MarcFinns/AtmoScan/__ATMOSCAN_MASTER_V3.3.1/ScreenWeatherStationSettings.h

/*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
  Adapted by Bodmer to use the faster TFT_eSPI library:
  https://github.com/Bodmer/TFT_eSPI

*/

#pragma once


// Setup
const int UPDATE_INTERVAL_SECS = 10 * 60; // Update every 10 minutes

// TimeClient settings
const float UTC_OFFSET = 0;

// Wunderground Settings, EDIT TO SUIT YOUR LOCATION
const bool IS_METRIC = true; // Temperature only? Wind speed units appear to stay in mph. To do: investigate <<<<<<<<<<<<<<<<<<<<<<<<<
//const String WUNDERGRROUND_LANGUAGE PROGMEM = "EN";

// Windspeed conversion, use 1 pair of #defines. To do: investigate a more convenient method <<<<<<<<<<<<<<<<<<<<<
//#define WIND_SPEED_SCALING 1.0      // mph
//#define WIND_SPEED_UNITS " mph"

//#define WIND_SPEED_SCALING 0.868976 // mph to knots
//#define WIND_SPEED_UNITS " kn"

#define WIND_SPEED_SCALING 1.60934  // mph to kph
#define WIND_SPEED_UNITS " kph"

// List of 19 items, so that the downloader knows what to fetch
const char * const wundergroundIcons[] PROGMEM = {"chanceflurries", "chancerain", "chancesleet", "chancesnow", "clear", "cloudy", "flurries", "fog", "hazy", "mostlycloudy", "mostlysunny", "partlycloudy", "partlysunny", "rain", "sleet", "snow", "sunny", "tstorms", "unknown"};

const char URL1[] PROGMEM = "http://www.squix.org/blog/wunderground/";
const char URL2[] PROGMEM = "http://www.squix.org/blog/wunderground/mini/";
const char URL3[] PROGMEM = "http://www.squix.org/blog/moonphase_L";
const char FILETYPE[] PROGMEM = ".bmp";
const char MOON[] PROGMEM = "/moon";
const char MINI[] PROGMEM = "/mini/";



/***************************
   End Settings
 **************************/

// #endif
