MarcFinns/AtmoScan/__ATMOSCAN_MASTER_V3.3.1/ScreenWeatherStation.cpp

/*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
  Adapted by Bodmer to use the faster TFT_eSPI library:
  https://github.com/Bodmer/TFT_eSPI

  Plus:
  Minor changes to text placement and auto-blanking out old text with background colour padding
  Moon phase text added
  Forecast text lines are automatically split onto two lines at a central space (some are long!)
  Time is printed with colons aligned to tidy display
  Min and max forecast temperatures spaced out
  The ` character has been changed to a degree symbol in the 36 point font
  New smart WU splash startup screen and updated progress messages
  Display does not need to be blanked between updates
  Icons nudged about slightly to add wind direction
*/

#include <Syslog.h>               // https://github.com/arcao/ESP8266_Syslog
#include <TFT_eSPI.h>             // https://github.com/Bodmer/TFT_eSPI
#include "ScreenWeatherStation.h"
#include "ScreenWeatherStationSettings.h"
#include "WundergroundClient.h"
#include "GlobalDefinitions.h"

// Fonts created by http://oleddisplay.squix.ch/
#include "Free_Fonts.h"
#include "Fonts.h"

// Download helper
#include "WebResource.h"

// External variables
extern Syslog syslog;
extern TFT_eSPI LCD;
extern GfxUi ui;
extern struct Configuration config;
extern struct ProcessContainer procPtr;
extern WebResource webResource;

// Prototypes
void errLog(String msg);
void setTurbo(bool setTurbo);
bool isTurbo();



// Static variables
bool ScreenWeatherStation::wunderValid = false;
WundergroundClient *ScreenWeatherStation::wunderground;

void  ScreenWeatherStation::activate()
{
#ifdef DEBUG_SYSLOG
  syslog.log(LOG_INFO, F("ScreenWeatherStation::activate()"));
#endif

  LCD.fillScreen(TFT_BLACK);
  LCD.setFreeFont(&ArialRoundedMTBold_14);
  LCD.setTextColor(TFT_ORANGE, TFT_BLACK);

  if (!procPtr.GeoLocation.isValid() || !config.connected)
  {
    LCD.setTextDatum(TC_DATUM);
    LCD.drawString(F("Weather Station needs"), 120, 120, GFXFF);
    LCD.drawString(F("network & geolocation"), 120, 140, GFXFF);
    isInitialised = false;
    return;
  }

  // Create Wunderground object if not existent
  if (!wunderValid)
  {

#ifdef DEBUG_SYSLOG
    syslog.log(LOG_INFO, F("wunderground object did not exist, initialise it"));
#endif

    // TURBO mode
    setTurbo(true);

    wunderground = new WundergroundClient(IS_METRIC);
    wunderValid = true;

    // Print credits
    LCD.setTextDatum(BC_DATUM);
    LCD.setTextColor(TFT_WHITE, TFT_BLACK);
    LCD.drawString(F("By: blog.squix.org"), 120, 180);
    LCD.drawString(F("Adapted: Bodmer, MarcFinns"), 120, 195);

    LCD.setTextColor(TFT_ORANGE, TFT_BLACK);
    LCD.setFreeFont(&ArialRoundedMTBold_14);
    LCD.drawString(F("Downloading resources..."), 120, 220);

    // Splash screen - Download WU graphic jpeg first and display it, then the Earth view
    webResource.downloadFile(F("http://i.imgur.com/njl1pMj.jpg"), F("/wunder.jpg"));
    if (SPIFFS.exists(F("/wunder.jpg")) == true) ui.drawJpeg(F("/wunder.jpg"), 0, 10);

    //  webResource.downloadFile(F("http://i.imgur.com/v4eTLCC.jpg"), F("/Earth.jpg"));
    webResource.downloadFile(F("http://i.imgur.com/v4eTLCC.jpg"), F("/Earth.jpg"));
    if (SPIFFS.exists(F("/Earth.jpg")) == true) ui.drawJpeg(F("/Earth.jpg"), 0, 320 - 56);

    // Download all icons from the net. If images already exist in SPIFFS don't download
    downloadResources();

    LCD.setTextPadding(240); // Pad next drawString() text to full width to over-write old text
    LCD.drawString(F("Fetching weather data..."), 120, 220);

    // load the weather information
    updateData();

    firstRun = false;

    // NORMAL mode
    setTurbo(false);

  }
  else
  {
#ifdef DEBUG_SYSLOG
    syslog.log(LOG_INFO, F("wunderground object being reused"));
#endif

    // No need to show splash screen
    firstRun = false;

    // Redraw screen
    drawCurrentWeather();
    drawForecast();
    drawAstronomy();
  }

  isInitialised = true;
}


void ScreenWeatherStation::update()
{
#ifdef DEBUG_SYSLOG
  syslog.log(LOG_INFO, F("ScreenWeatherStation update()"));
#endif

  // If not valid conditions, do nothing!
  if (!isInitialised || !procPtr.GeoLocation.isValid() || !config.connected)
  {
#ifdef DEBUG_SERIAL
    syslog.log(LOG_DEBUG, F("WeatherStation - not valid preconditions, can't run " ));
#endif
    return;
  }

  // Check if we should update weather information
  updateData();
}


// Download the bitmaps
void ScreenWeatherStation::downloadResources()
{

  // Download resources
  char id[5];
  char urlBuffer[100];
  char fileNameBuffer[100];

  int totalFiles = 19 + 19 + 24;

  for (int i = 0; i < 19; i++)
  {
    sprintf(id, "%02d", i);

    // Prepare URL
    strcpy_P(urlBuffer, URL1);
    strcat_P(urlBuffer, wundergroundIcons[i]);
    strcat_P(urlBuffer, FILETYPE);

    // Prepare filename
    strcpy_P(fileNameBuffer, wundergroundIcons[i]);
    strcat_P(fileNameBuffer, FILETYPE);

    // Download resource
    webResource.downloadFile(urlBuffer, fileNameBuffer);
  }

  for (int i = 0; i < 19; i++)
  {
    sprintf(id, "%02d", i);

    // Prepare URL
    strcpy_P(urlBuffer, URL2);
    strcat_P(urlBuffer, wundergroundIcons[i]);
    strcat_P(urlBuffer, FILETYPE);

    // Prepare filename
    strcpy_P(fileNameBuffer, MINI);
    strcat_P(fileNameBuffer, wundergroundIcons[i]);
    strcat_P(fileNameBuffer, FILETYPE);

    // Download resource
    webResource.downloadFile(urlBuffer, fileNameBuffer);

  }

  for (int i = 0; i < 24; i++)
  {
    // Prepare URL
    strcpy_P(urlBuffer, URL3);
    dtostrf(i, 1, 0, &urlBuffer[strlen(urlBuffer)]);
    strcat_P(urlBuffer, FILETYPE);

    // Prepare filename
    strcpy_P(fileNameBuffer, MOON);
    dtostrf(i, 1, 0, &fileNameBuffer[strlen(fileNameBuffer)]);
    strcat_P(fileNameBuffer, FILETYPE);

    // Download resource
    webResource.downloadFile(urlBuffer, fileNameBuffer);

    // webResource.downloadFile("http://www.squix.org/blog/moonphase_L" + String(i) + ".bmp", "/moon" + String(i) + ".bmp");
  }
}

// Update the internet based information and update screen
void ScreenWeatherStation::updateData()
{
  // firstRun = true;  // Test only
  // firstRun = false; // Test only
#ifdef DEBUG_SERIAL
  Serial.println("WeatherStation - updating data");
#endif

  // Check if we should update weather information
  // Update only if:
  if ((firstRun) // First time
      || (wunderground->isValid && (millis() - wunderground->lastDownloadUpdate > 1000 * UPDATE_INTERVAL_SECS)) // If valid, every given interval
      || (!wunderground->isValid && (millis() - wunderground->lastDownloadUpdate > 60000))) // if not valid, retry after 1 minute
  {
#ifdef DEBUG_SYSLOG
    syslog.log(LOG_DEBUG, String(F("#### WEATHER DATA NEED UPDATE, IS ")) + String((millis() - wunderground->lastDownloadUpdate ) / 1000) + F(" SECONDS OLD"));
#endif


    // Set location only once (does not change)
    if (firstRun)
    {
      drawProgress(20, F("Setting location..."));
    }

    if (firstRun
        || !wunderground->isValid)
    {
      wunderground->isValid = wunderground->updateLocation(config.wunderground_key,
                              procPtr.GeoLocation.getLatitude(),
                              procPtr.GeoLocation.getLongitude());
    }

    // Conditions
    if (wunderground->isValid)
    {
      if (firstRun)
        drawProgress(40, F("Updating conditions..."));
      else
        ui.fillSegment(120, 160, 0, (int) (25 * 3.6), 24, TFT_RED);
      wunderground->isValid = wunderground->updateConditions(config.wunderground_key, F("EN"), wunderground->getCountryName(), wunderground->getCity());
    }

    // Forecast
    if (wunderground->isValid)
    {
      if (firstRun)
        drawProgress(60, F("Updating forecast..."));
      else
        ui.fillSegment(120, 160, 0, (int) (50 * 3.6), 24, TFT_RED);
      wunderground->isValid = wunderground->updateForecast(config.wunderground_key, F("EN"), wunderground->getCountryName(), wunderground->getCity());
    }

    // Astronomy
    if (wunderground->isValid)
    {

      if (firstRun)
        drawProgress(80, F("Updating astronomy..."));
      else
        ui.fillSegment(120, 160, 0, (int) (75 * 3.6), 24, TFT_RED);
      wunderground->isValid = wunderground->updateAstronomy(config.wunderground_key, F("EN"), wunderground->getCountryName(), wunderground->getCity());
    }


    if (firstRun)
      drawProgress(100, F("Done..."));
    else
      ui.fillSegment(120, 160, 0, 360, 24, TFT_RED);

    if (firstRun) delay(100);

    // Clear screen
    if (firstRun) LCD.fillScreen(TFT_BLACK);
    else
      // Erase progress pie..
      ui.fillSegment(120, 160, 0, 360, 24, TFT_BLACK);


#ifdef DEBUG_SYSLOG
    syslog.log(LOG_DEBUG, String(F("1 = ")) + wunderground->getCountry());
    syslog.log(LOG_DEBUG, String(F("2 = ")) + wunderground->getCountryName());
    syslog.log(LOG_DEBUG, String(F("3 = ")) + wunderground->getCity());
    syslog.log(LOG_DEBUG, String(F("4 = ")) + wunderground->getTZ_Short());
    syslog.log(LOG_DEBUG, String(F("5 = ")) + wunderground->getTZ_Long());
#endif

    // Redraw all
    drawCurrentWeather();
    drawForecast();
    drawAstronomy();

    //if (firstRun) screenshotToConsole(); // Weather screen dump. Not supported in this sketch
    firstRun = false;

    wunderground->lastDownloadUpdate = millis();
  }
  else
  {

#ifdef DEBUG_SYSLOG
    syslog.log(LOG_DEBUG, String(F("#### WEATHER DATA _DOES_NOT_ NEED UPDATE, IS ")) + String((millis() - wunderground->lastDownloadUpdate) / 1000) + F(" SECONDS OLD"));
#endif
    return;
  }
}

// Progress bar helper
void ScreenWeatherStation::drawProgress(uint8_t percentage, String text)
{
  LCD.setFreeFont(&ArialRoundedMTBold_14);

  LCD.setTextDatum(BC_DATUM);
  LCD.setTextColor(TFT_ORANGE, TFT_BLACK);
  LCD.setTextPadding(240);
  LCD.drawString(text, 120, 220);

  ui.drawProgressBar(10, 225, 240 - 20, 15, percentage, TFT_WHITE, TFT_BLUE);

  LCD.setTextPadding(0);
}


// draws current weather information
void ScreenWeatherStation::drawCurrentWeather()
{
  // Weather Icon
  String weatherIcon = getMeteoconIcon(wunderground->getTodayIcon());
  //uint32_t dt = millis();
  ui.drawBmp(weatherIcon + F(".bmp"), 0, 64);

  // Weather Text
  String weatherText = wunderground->getWeatherText();
  //weatherText = "Heavy Thunderstorms with Small Hail"; // Test line splitting with longest(?) string


#ifdef DEBUG_SERIAL
  Serial.println(wunderground->getWeatherText());
#endif

  LCD.setFreeFont(&ArialRoundedMTBold_14);

  LCD.setTextDatum(BR_DATUM);
  LCD.setTextColor(TFT_ORANGE, TFT_BLACK);

  int splitPoint = 0;
  int xpos = 230;
  splitPoint =  ui.splitIndex(weatherText);
  if (splitPoint > 16) xpos = 235;

  LCD.setTextPadding(LCD.textWidth(F(" Heavy Thunderstorms")));  // Max anticipated string width + margin
  if (splitPoint) LCD.drawString(weatherText.substring(0, splitPoint), xpos, 83);
  LCD.setTextPadding(LCD.textWidth(F(" with Small Hail")));  // Max anticipated string width + margin
  LCD.drawString(weatherText.substring(splitPoint), xpos, 98);

  LCD.setFreeFont(&ArialRoundedMTBold_36);

  LCD.setTextDatum(TR_DATUM);
  LCD.setTextColor(TFT_ORANGE, TFT_BLACK);
  LCD.setTextPadding(LCD.textWidth(F("-88`")));

  // Font ASCII code 96 (0x60) modified to make "`" a degree symbol
  weatherText = wunderground->getCurrentTemp();
  if (weatherText.indexOf(F("."))) weatherText = weatherText.substring(0, weatherText.indexOf(F("."))); // Make it integer temperature
  if (weatherText == F("")) weatherText = F("?");  // Handle null return
  LCD.drawString(weatherText + F("`"), 221, 100);

  LCD.setFreeFont(&ArialRoundedMTBold_14);

  LCD.setTextDatum(TL_DATUM);
  LCD.setTextPadding(0);
  if (IS_METRIC) LCD.drawString(F("C "), 221, 100);
  else  LCD.drawString(F("F "), 221, 100);

  weatherText = wunderground->getWindDir() + F(" ");
  weatherText += String((int)(wunderground->getWindSpeed().toInt() * WIND_SPEED_SCALING)) + WIND_SPEED_UNITS;

  LCD.setTextPadding(LCD.textWidth(F("Variable 888 mph "))); // Max string length?
  LCD.drawString(weatherText, 114, 136);

  weatherText = wunderground->getWindDir();

  int windAngle = 0;
  String compassCardinal = F("");
  switch (weatherText.length())
  {
    case 1:
      compassCardinal = F("N E S W "); // Not used, see default below
      windAngle = 90 * compassCardinal.indexOf(weatherText) / 2;
      break;
    case 2:
      compassCardinal = F("NE SE SW NW");
      windAngle = 45 + 90 * compassCardinal.indexOf(weatherText) / 3;
      break;
    case 3:
      compassCardinal = F("NNE ENE ESE SSE SSW WSW WNW NNW");
      windAngle = 22 + 45 * compassCardinal.indexOf(weatherText) / 4; // Should be 22.5 but accuracy is not needed!
      break;
    default:
      if (weatherText == F("Variable")) windAngle = -1;
      else {
        compassCardinal = F("North East  South West"); // Possible strings
        windAngle = 90 * compassCardinal.indexOf(weatherText) / 6;
      }
      break;
  }

  LCD.fillCircle(128, 110, 23, TFT_BLACK); // Erase old plot, radius + 1 to delete stray pixels
  LCD.drawCircle(128, 110, 6, TFT_RED);
  if ( windAngle >= 0 ) ui.fillSegment(128, 110, windAngle - 15, 30, 22, TFT_GREEN); // Might replace this with a bigger rotating arrow
  //LCD.drawCircle(128, 110, 22, TFT_DARKGREY);    // Outer ring - optional

  ui.drawSeparator(153);

  LCD.setTextPadding(0); // Reset padding width to none
}

// draws the three forecast columns
void ScreenWeatherStation::drawForecast()
{
  drawForecastDetail(10, 171, 0);
  drawForecastDetail(95, 171, 2);
  drawForecastDetail(180, 171, 4);
  ui.drawSeparator(171 + 69);
}

// helper for the forecast columns
void ScreenWeatherStation::drawForecastDetail(uint16_t x, uint16_t y, uint8_t dayIndex)
{
  LCD.setFreeFont(&ArialRoundedMTBold_14);

  String day = wunderground->getForecastTitle(dayIndex).substring(0, 3);
  day.toUpperCase();

  LCD.setTextDatum(BC_DATUM);

  LCD.setTextColor(TFT_ORANGE, TFT_BLACK);
  LCD.setTextPadding(LCD.textWidth(F("WWW")));
  LCD.drawString(day, x + 25, y);

  LCD.setTextColor(TFT_WHITE, TFT_BLACK);
  LCD.setTextPadding(LCD.textWidth(F("-88   -88")));
  LCD.drawString(wunderground->getForecastHighTemp(dayIndex) + F("   ") + wunderground->getForecastLowTemp(dayIndex), x + 25, y + 14);

  String weatherIcon = getMeteoconIcon(wunderground->getForecastIcon(dayIndex));

#ifdef DEBUG_SYSLOG
  syslog.log(LOG_DEBUG, String(F("icon is = /mini/")) + weatherIcon + F(".bmp"));
#endif

  ui.drawBmp(String(F("/mini/")) + weatherIcon + F(".bmp"), x, y + 15);


  LCD.setTextPadding(0); // Reset padding width to none
}

// draw moonphase and sunrise/set and moonrise/set
void ScreenWeatherStation::drawAstronomy()
{
  LCD.setFreeFont(&ArialRoundedMTBold_14);

  LCD.setTextDatum(BC_DATUM);
  LCD.setTextColor(TFT_ORANGE, TFT_BLACK);
  LCD.setTextPadding(LCD.textWidth(F(" Waxing Crescent ")));
  LCD.drawString(wunderground->getMoonPhase(), 120, 260 - 2);

  int moonAgeImage = 24 * wunderground->getMoonAge().toInt() / 30.0;
  ui.drawBmp(String(F("/moon")) + String(moonAgeImage) + F(".bmp"), 120 - 30, 260);

  LCD.setTextDatum(BC_DATUM);
  LCD.setTextColor(TFT_ORANGE, TFT_BLACK);
  LCD.setTextPadding(0); // Reset padding width to none
  LCD.drawString(F("Sun"), 40, 280);

  LCD.setTextDatum(BR_DATUM);
  LCD.setTextColor(TFT_WHITE, TFT_BLACK);
  LCD.setTextPadding(LCD.textWidth(F(" 88:88 ")));
  int dt = ui.rightOffset(wunderground->getSunriseTime(), F(":")); // Draw relative to colon to them aligned
  LCD.drawString(wunderground->getSunriseTime(), 40 + dt, 300);

  dt = ui.rightOffset(wunderground->getSunsetTime(), F(":"));
  LCD.drawString(wunderground->getSunsetTime(), 40 + dt, 315);

  LCD.setTextDatum(BC_DATUM);
  LCD.setTextColor(TFT_ORANGE, TFT_BLACK);
  LCD.setTextPadding(0); // Reset padding width to none
  LCD.drawString(F("Moon"), 200, 280);

  LCD.setTextDatum(BR_DATUM);
  LCD.setTextColor(TFT_WHITE, TFT_BLACK);
  LCD.setTextPadding(LCD.textWidth(F(" 88:88 ")));
  dt = ui.rightOffset(wunderground->getMoonriseTime(), F(":")); // Draw relative to colon to them aligned
  LCD.drawString(wunderground->getMoonriseTime(), 200 + dt, 300);

  dt = ui.rightOffset(wunderground->getMoonsetTime(), F(":"));
  LCD.drawString(wunderground->getMoonsetTime(), 200 + dt, 315);

  LCD.setTextPadding(0); // Reset padding width to none
}


// Helper function, should be part of the weather station library and should disappear soon
String ScreenWeatherStation::getMeteoconIcon(String iconText)
{
  if (iconText == F("F")) return F("chanceflurries");
  if (iconText == F("Q")) return F("chancerain");
  if (iconText == F("W")) return F("chancesleet");
  if (iconText == F("V")) return F("chancesnow");
  if (iconText == F("S")) return F("chancestorms");
  if (iconText == F("B")) return F("clear");
  if (iconText == F("Y")) return F("cloudy");
  if (iconText == F("F")) return F("flurries");
  if (iconText == F("M")) return F("fog");
  if (iconText == F("E")) return F("hazy");
  if (iconText == F("Y")) return F("mostlycloudy");
  if (iconText == F("H")) return F("mostlysunny");
  if (iconText == F("H")) return F("partlycloudy");
  if (iconText == F("J")) return F("partlysunny");
  if (iconText == F("W")) return F("sleet");
  if (iconText == F("R")) return F("rain");
  if (iconText == F("W")) return F("snow");
  if (iconText == F("B")) return F("sunny");
  if (iconText == F("0")) return F("tstorms");

  return F("unknown");
}

void ScreenWeatherStation::deactivate()
{
#ifdef DEBUG_SYSLOG
  syslog.log(LOG_INFO, F("ScreenWeatherStation::deactivate()"));
#endif

}


bool ScreenWeatherStation::onUserEvent(int event)
{
  return false;
}

long ScreenWeatherStation::getRefreshPeriod()
{
  return 5000;
}

String ScreenWeatherStation::getScreenName()
{
  return F("Weather Station");
}

bool ScreenWeatherStation::isFullScreen()
{
  return false;
}

bool ScreenWeatherStation::getRefreshWithScreenOff()
{
  return false;
}
