MarcFinns/AtmoScan/__ATMOSCAN_MASTER_V3.3.1/ScreenPlaneSpotter.h

/********************************************************/
/*                    ATMOSCAN                          */
/*                                                      */
/*            Author: Marc Finns 2017                   */
/*                                                      */
/********************************************************/

#pragma once

#include "Screen.h"
#include "GeoMap.h"
#include "PlaneSpotter.h"
#include "GlobalDefinitions.h"


// External variables
extern TFT_eSPI LCD;
extern struct Configuration config;

// Screen Handler definition
class ScreenPlaneSpotter: public Screen
{
  public:
    // Call the Process constructor
    ScreenPlaneSpotter(): geoMap(MapProvider::Google, config.google_key, MAP_WIDTH, MAP_HEIGHT),
      planeSpotter(&LCD, &geoMap) {};
    virtual ~ScreenPlaneSpotter() {};
    virtual void activate();
    virtual void update();
    virtual void deactivate();
    virtual bool onUserEvent(int event);
    virtual long getRefreshPeriod();
    virtual String getScreenName();
    virtual bool isFullScreen();
    virtual bool getRefreshWithScreenOff();
    bool isInitialised = false;

  private:
    GeoMap geoMap;
    PlaneSpotter planeSpotter;
    Coordinates mapCenter;
    Coordinates northWestBound;
    Coordinates southEastBound;
    static bool firstRun;
    void removeAllMaps();
};


const uint8_t plane_splash[] PROGMEM = {
  0xff, 0xd8, 0xff, 0xe0, 0x00, 0x10, 0x4a, 0x46, 0x49, 0x46, 0x00, 0x01,
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
  0x75, 0x0b, 0xf4, 0x75, 0x20, 0xc9, 0x6a, 0x5d, 0xa9, 0x0f, 0x6d, 0x8d,
  0xa0, 0x4b, 0x6b, 0x3d, 0x83, 0x17, 0x7b, 0x99, 0x10, 0x0f, 0x0f, 0x4a,
  0x91, 0xa6, 0x58, 0xd9, 0x5b, 0xa5, 0x80, 0xe7, 0x2e, 0x3e, 0x18, 0xf1,
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
};
const unsigned int plane_splash_len = 18699;
