MarcFinns/AtmoScan/__ATMOSCAN_MASTER_V3.3.1/ScreenLowbatt.h

/********************************************************/
/*                    ATMOSCAN                          */
/*                                                      */
/*            Author: Marc Finns 2017                   */
/*                                                      */
/********************************************************/

#pragma once

#include "Screen.h"

// Screen Handler definition
class ScreenLowbatt: public Screen
{
  public:
    // Call the Process constructor
    ScreenLowbatt() {}
    virtual ~ScreenLowbatt() {}
    virtual void activate();
    virtual void update();
    virtual void deactivate();
    virtual bool onUserEvent(int event);
    virtual long getRefreshPeriod();
    virtual String getScreenName();
    virtual bool isFullScreen();
    virtual bool getRefreshWithScreenOff();
};


// Generated by   : ImageConverter 565 Online
// Generated from : BatteryLow.jpg
// Time generated : Wed, 30 Aug 17 01:01:55 +0200  (Server timezone: CET)
// Image Size     : 185x147 pixels
// Memory usage   : 54390 bytes


// Icon width and height
const uint16_t batteryLowWidth = 185;
const uint16_t batteryLowHeight = 147;

const unsigned short batteryLowIcon[27195] PROGMEM = {
  0x0000, 0x0000, 0x0000, 0x0000, 0x0000, 0x0000, 0x0020, 0x0020, 0x0020, 0x0020, 0x0020, 0x0020, 0x0020, 0x0020, 0x0020, 0x0020,   // 0x0010 (16) pixels
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
  0x10A3, 0x10C2, 0x10C2, 0x10A3, 0x10C3, 0x10C3, 0x10C3, 0x10C3, 0x10C3, 0x10C2, 0x10C2, 0x10A3, 0x10A3, 0x10C2, 0x10C3, 0x10C3,   // 0x2F80 (12160) pixels
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
