MarcFinns/AtmoScan/__ATMOSCAN_MASTER_V3.3.1/ScreenSetup.h

/********************************************************/
/*                    ATMOSCAN                          */
/*                                                      */
/*            Author: Marc Finns 2017                   */
/*                                                      */
/********************************************************/


#pragma once

#include "Screen.h"

// Screen Handler definition
class ScreenSetup: public Screen
{
  public:
    // Call the Process constructor
    ScreenSetup() {}
    virtual ~ScreenSetup() {}
    virtual void activate();
    virtual void update();
    virtual void deactivate();
    virtual bool onUserEvent(int event);
    virtual long getRefreshPeriod();
    virtual String getScreenName();
    virtual bool isFullScreen();
    virtual bool getRefreshWithScreenOff();

  private:
    static void saveConfigCallback();
    void  startHotspot();
};


// ********** Wifi hotspot symbol
// Generated by   : ImageConverter 565 Online
// http://www.rinkydinkelectronics.com/t_imageconverter565.php
// Generated from : wifi symbol5 SMALL.gif
// Time generated : Sat, 19 Aug 17 16:41:18 +0200  (Server timezone: CET)
// Image Size     : 120x129 pixels
// Memory usage   : 30960 bytes

// Icon width and height
const uint16_t hotspotWidth = 120;
const uint16_t hotspotHeight = 129;

const unsigned short hotspot[15480] PROGMEM = {
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
  0x013F, 0x013F, 0x013F, 0x013F, 0x013F, 0x013F, 0x013F, 0x013F, 0x013F, 0x013F, 0x013F, 0x013F, 0x013F, 0x013F, 0x013F, 0x013F,   // 0x2730 (10032) pixels
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
